blonski3/ibm-modern-m-ssk/docs/FSSK v1.00/Design 1.00.ods

Sheet: v0.16
 |  | Row 1 |  | Row 2 |  | Row 3 |  | Row 4 |  | Row 5 |  | Row 6 |  | Concatenate |  |  |  | Keys in columns
xwhatsit row |  | 10 | 9 | 9 | 8 | 6 | 7 | 5 | 6 | 4 | 3 | 3 | 4 |  |  | Total | Total | 3 | 4 | 5 | 6 | 7 | 8 | 9 | 10
13 | Matrix | 10 |  | 9 |  |  | 7 | 5 | 6 | 4 |  | 3 |  | 10 9 7 5 6 4 3 | 13 | 7 | 7 | 1 | 1 | 1 | 1 | 1 | 0 | 1 | 1
13 | Key | ESC |  | ~ |  |  | TAB | CAPS | A | L-SHIFT |  | L-CTR |  | ESC ~ TAB CAPS A L-SHIFT L-CTR
14 | Matrix | 10 |  | 9 | 8 | 6 | 7 | 5 |  | 4 | 3 |  |  | 10 9 8 6 7 5 4 3 | 14 | 8 | 8 | 1 | 1 | 1 | 1 | 1 | 1 | 1 | 1
14 | Key | F1 |  | 1 | 2 | Q | W | S |  | Z | ISO 102 |  |  | F1 1 2 Q W S Z ISO 102
15 | Matrix | 10 |  | 9 | 8 |  | 7 | 5 |  | 4 |  | 3 |  | 10 9 8 7 5 4 3 | 15 | 7 | 7 | 1 | 1 | 1 | 0 | 1 | 1 | 1 | 1
15 | Key | F2 |  | 3 | 4 |  | E | D |  | X |  | L-ALT |  | F2 3 4 E D X L-ALT
16 | Matrix | 10 | 9 |  | 8 |  | 7 | 5 | 6 | 4 | 3 |  |  | 10 9 8 7 5 6 4 3 | 16 | 8 | 8 | 1 | 1 | 1 | 1 | 1 | 1 | 1 | 1
16 | Key | F3 | F4 |  | 5 |  | R | F | G | V | C |  |  | F3 F4 5 R F G V C
17 | Matrix | 10 |  | 9 | 8 | 6 | 7 | 5 |  | 4 | 3 |  |  | 10 9 8 6 7 5 4 3 | 17 | 8 | 8 | 1 | 1 | 1 | 1 | 1 | 1 | 1 | 1
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
